henryka-audio/thespeaker/Images/Parts/USB-C_charger_board.JPG

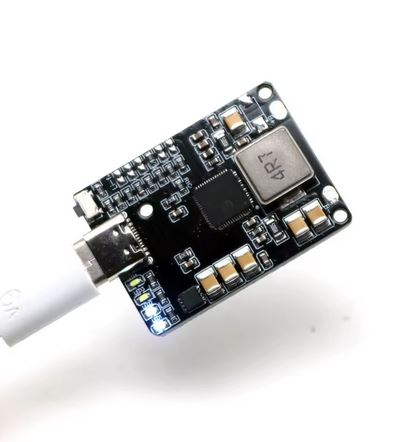
Images/Parts/USB-C_charger_board.JPG
